birk12/3d-Printing-AIR-CHECK/cad/drawings/bottom_view.png

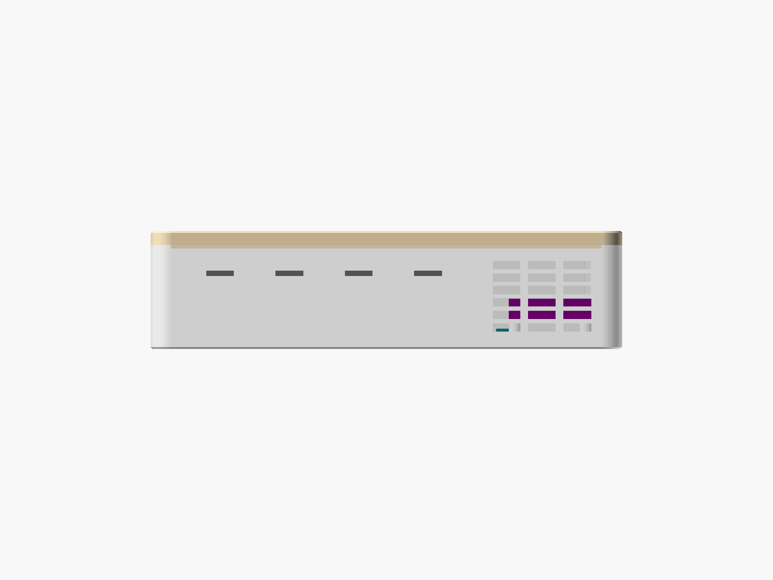
cad/drawings/bottom_view.png
