birk12/3d-Printing-AIR-CHECK/cad/drawings/top_view.png

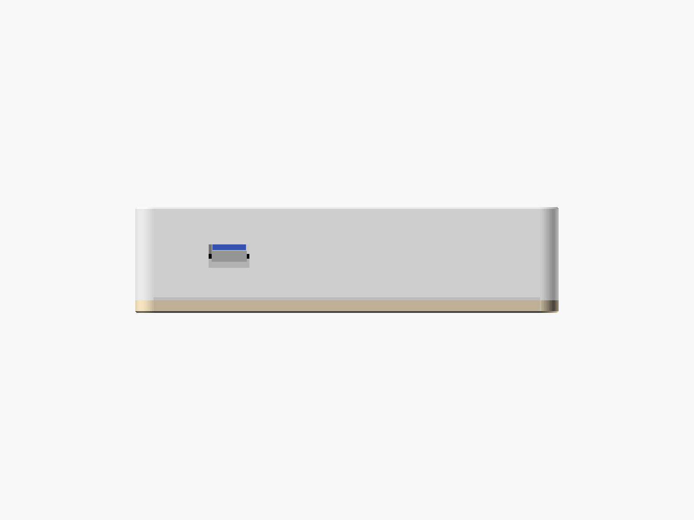
cad/drawings/top_view.png
