birk12/3d-Printing-AIR-CHECK/cad/drawings/xray_back.png

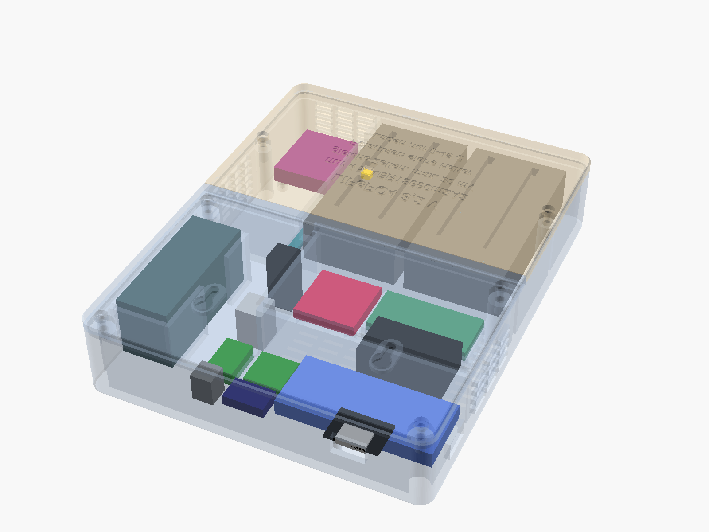
cad/drawings/xray_back.png
