birk12/3d-Printing-AIR-CHECK/cad/drawings/assembly_iso.png

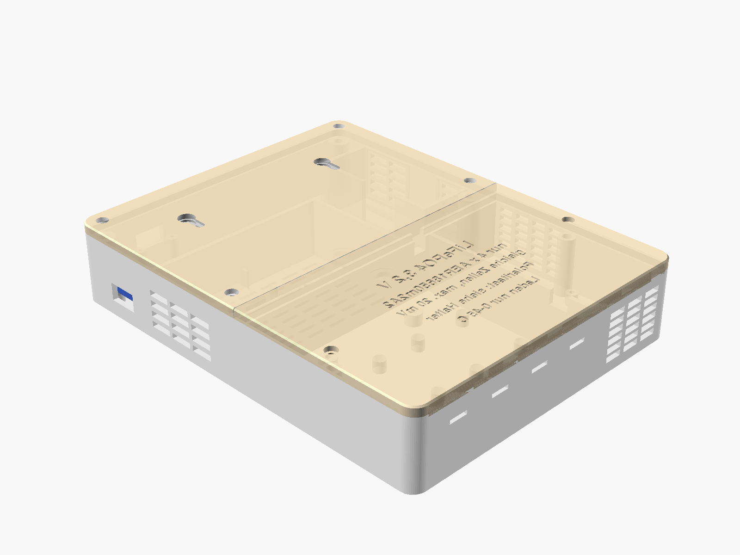
cad/drawings/assembly_iso.png
