birk12/3d-Printing-AIR-CHECK/firmware/components/ac_hal/src/button.c

/* One multifunction button on GPIO1, active low.
 *
 *   short press   (< 3 s)        show the air quality on the LED
 *   long press    (3 .. 8 s)     open commissioning
 *   calibrate     (8 .. 12 s)    fresh-air CO2 calibration (take it outdoors)
 *   very long     (12 .. 20 s)   factory reset
 *   over 20 s                    ignored, so a jammed button cannot wipe the
 *                                device
 *
 * While it is held, the LED shows what letting go would do (ac_status).
 * GPIO1 is an LP pad on the ESP32-C6, so it can also wake the chip.
 */
#include "ac_hal/ac_hal.h"

#include "driver/gpio.h"
#include "esp_log.h"
#include "esp_timer.h"
#include "freertos/FreeRTOS.h"
#include "freertos/task.h"

static const char *TAG = "button";
static int64_t s_down_us;
static bool s_was_down;

esp_err_t ac_button_init(void)
{
    gpio_config_t io = {
        .pin_bit_mask = 1ULL << AC_PIN_BUTTON,
        .mode = GPIO_MODE_INPUT,
        .pull_up_en = GPIO_PULLUP_ENABLE,   /* the board has 100k as well */
        .intr_type = GPIO_INTR_DISABLE,
    };
    return gpio_config(&io);
}

bool ac_button_pressed(void) { return gpio_get_level(AC_PIN_BUTTON) == 0; }

uint32_t ac_button_held_ms(void)
{
    if (!s_was_down || !ac_button_pressed()) return 0;
    return (uint32_t)((esp_timer_get_time() - s_down_us) / 1000);
}

ac_button_event_t ac_button_poll(void)
{
    bool down = ac_button_pressed();
    int64_t now = esp_timer_get_time();

    if (down && !s_was_down) {
        s_down_us = now;
        s_was_down = true;
        return AC_BTN_NONE;
    }
    if (!down && s_was_down) {
        s_was_down = false;
        uint32_t held = (uint32_t)((now - s_down_us) / 1000);
        if (held < 40) return AC_BTN_NONE;              /* contact bounce */
        if (held > AC_HOLD_ABORT_MS) {
            ESP_LOGW(TAG, "held %lu ms, ignoring", (unsigned long)held);
            return AC_BTN_NONE;
        }
        if (held >= AC_HOLD_RESET_MS) return AC_BTN_VERY_LONG;
        if (held >= AC_HOLD_CALIBRATE_MS) return AC_BTN_CALIBRATE;
        if (held >= AC_HOLD_PAIRING_MS) return AC_BTN_LONG;
        return AC_BTN_SHORT;
    }
    return AC_BTN_NONE;
}
